gpc123456/SmartClock/GUI_Picture/ConfigWiFiSuccess.bmp

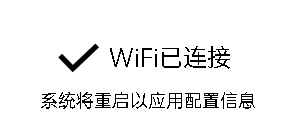
GUI_Picture/ConfigWiFiSuccess.bmp
