gpc123456/SmartClock/GUI_Picture/Pomodoro_HomePage.bmp

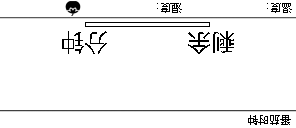
GUI_Picture/Pomodoro_HomePage.bmp
