gpc123456/SmartClock/GUI_Picture/Pomodoro_StartPage.bmp

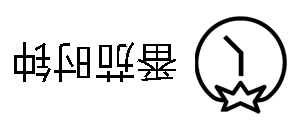
GUI_Picture/Pomodoro_StartPage.bmp
