gpc123456/SmartClock/GUI_Picture/StartPage.bmp

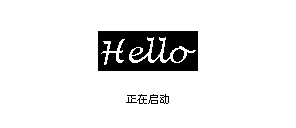
GUI_Picture/StartPage.bmp
