gpc123456/SmartClock/src/TimeNumber.h

#ifndef TIMENUMBER_H
#define TIMENUMBER_H

#include <Arduino.h>

const PROGMEM uint8_t Num_0[]={
 /* 0X81,0X01,0X28,0X00,0X40,0X00, */
0XFF,0XFF,0XFF,0XFF,0XFF,0XFF,0XFF,0XFF,0XFF,0XFF,0XFF,0X80,0X01,0XFF,0XFF,0XFF,
0XFF,0XFF,0XE0,0X00,0X00,0X07,0XFF,0XFF,0XFF,0XFE,0X00,0X00,0X00,0X00,0XFF,0XFF,
0XFF,0XF8,0X00,0X00,0X00,0X00,0X1F,0XFF,0XFF,0XE0,0X00,0X00,0X00,0X00,0X07,0XFF,
0XFF,0X80,0X00,0X1F,0XF0,0X00,0X01,0XFF,0XFF,0X00,0X0F,0XFF,0XFF,0XF0,0X00,0XFF,
0XFE,0X00,0XFF,0XFF,0XFF,0XFF,0X00,0X7F,0XFC,0X03,0XFF,0XFF,0XFF,0XFF,0XC0,0X3F,
0XF8,0X0F,0XFF,0XFF,0XFF,0XFF,0XF0,0X1F,0XF0,0X1F,0XFF,0XFF,0XFF,0XFF,0XF8,0X1F,
0XF0,0X3F,0XFF,0XFF,0XFF,0XFF,0XFC,0X0F,0XE0,0X7F,0XFF,0XFF,0XFF,0XFF,0XFE,0X0F,
0XE0,0XFF,0XFF,0XFF,0XFF,0XFF,0XFF,0X07,0XE0,0XFF,0XFF,0XFF,0XFF,0XFF,0XFF,0X07,
0XC1,0XFF,0XFF,0XFF,0XFF,0XFF,0XFF,0X87,0XC1,0XFF,0XFF,0XFF,0XFF,0XFF,0XFF,0X83,
0XC1,0XFF,0XFF,0XFF,0XFF,0XFF,0XFF,0X83,0XC1,0XFF,0XFF,0XFF,0XFF,0XFF,0XFF,0X83,
0XC1,0XFF,0XFF,0XFF,0XFF,0XFF,0XFF,0X83,0XC1,0XFF,0XFF,0XFF,0XFF,0XFF,0XFF,0X83,
0XC1,0XFF,0XFF,0XFF,0XFF,0XFF,0XFF,0X83,0XC1,0XFF,0XFF,0XFF,0XFF,0XFF,0XFF,0X83,
0XC1,0XFF,0XFF,0XFF,0XFF,0XFF,0XFF,0X87,0XE0,0XFF,0XFF,0XFF,0XFF,0XFF,0XFF,0X07,
0XE0,0XFF,0XFF,0XFF,0XFF,0XFF,0XFF,0X07,0XE0,0X7F,0XFF,0XFF,0XFF,0XFF,0XFE,0X0F,
0XF0,0X3F,0XFF,0XFF,0XFF,0XFF,0XFC,0X0F,0XF0,0X1F,0XFF,0XFF,0XFF,0XFF,0XF8,0X1F,
0XF8,0X0F,0XFF,0XFF,0XFF,0XFF,0XF0,0X1F,0XFC,0X03,0XFF,0XFF,0XFF,0XFF,0XC0,0X3F,
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
0X01,0XFF,0XF8,0X1F,0XFF,0XFF,0XF0,0X00,0X7F,0XF0,0X1F,0XFF,0XFF,0XFC,0X00,0X00,
0X00,0X3F,0XFF,0XFF,0XFF,0X00,0X00,0X00,0X7F,0XFF,0XFF,0XFF,0XC0,0X00,0X01,0XFF,
0XFF,0XFF,0XFF,0XF8,0X00,0X07,0XFF,0XFF,0XFF,0XFF,0XFF,0X00,0X3F,0XFF,0XFF,0XFF,
0XFF,0XFF,0XFF,0XFF,0XFF,};

#endif
