gpc123456/SmartClock/src/WeatherIcon.h

#ifndef WEATHERICON_H
#define WEATHERICON_H

#include <Arduino.h>

const PROGMEM uint8_t WCode_0[]={
/* 0X81,0X01,0X32,0X00,0X30,0X00, */
0XFF,0XFF,0XFF,0XFF,0XFF,0XFF,0XFF,0XFF,0XFF,0XFF,0XFF,0XFF,0XFF,0XFF,0XFF,0XFF,
0XFF,0XFF,0XFF,0XFF,0XFF,0XFF,0XFF,0XFF,0XFF,0XFF,0XFF,0XFF,0XFF,0XFF,0XFF,0XFF,
0XFF,0XFF,0XFF,0XFF,0XFF,0XFF,0XFF,0XFF,0XFF,0XFF,0XFF,0XF0,0X01,0XFF,0XFF,0XFF,
0XFF,0XC0,0X00,0X7F,0XFF,0XFF,0XFF,0X00,0X00,0X1F,0XFF,0XFF,0XFE,0X00,0X00,0X0F,
0XFF,0XFF,0XF8,0X00,0X00,0X03,0XFF,0XFF,0XF0,0X00,0X00,0X01,0XFF,0XFF,0XF0,0X00,
0X00,0X01,0XFF,0XFF,0XE0,0X00,0X00,0X00,0XFF,0XFF,0XC0,0X00,0X00,0X00,0X7F,0XFF,
0XC0,0X00,0X00,0X00,0X7F,0XFF,0X80,0X00,0X00,0X00,0X3F,0XFF,0X80,0X00,0X00,0X00,
0X3F,0XFF,0X00,0X00,0X00,0X00,0X1F,0XFF,0X00,0X00,0X00,0X00,0X1F,0XFF,0X00,0X00,
0X00,0X00,0X19,0X53,0X00,0X00,0X00,0X00,0X19,0X25,0X00,0X00,0X00,0X00,0X19,0X25,
0X00,0X00,0X00,0X00,0X10,0X27,0X00,0X00,0X00,0X00,0X19,0X27,0X00,0X00,0X00,0X00,
0X19,0X41,0X00,0X00,0X00,0X00,0X1F,0X7F,0X00,0X00,0X00,0X00,0X18,0X03,0X00,0X00,
0X00,0X00,0X1B,0XBB,0X80,0X00,0X00,0X00,0X38,0X03,0X80,0X00,0X00,0X00,0X3F,0XFF,
0XC0,0X00,0X00,0X00,0X7F,0XFF,0XC0,0X00,0X00,0X00,0X7F,0XFF,0XE0,0X00,0X00,0X00,
0XFF,0XFF,0XF0,0X00,0X00,0X01,0XFF,0XFF,0XF0,0X00,0X00,0X01,0XFF,0XFF,0XF8,0X00,
0X00,0X03,0XFF,0XFF,0XFE,0X00,0X00,0X0F,0XFF,0XFF,0XFF,0X00,0X00,0X1F,0XFF,0XFF,
0XFF,0XC0,0X00,0X7F,0XFF,0XFF,0XFF,0XF0,0X01,0XFF,0XFF,0XFF,0XFF,0XFF,0XFF,0XFF,
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
0XDE,0XFB,0XDE,0XFB,0XDE,0XFB,0XDE,0XFB,0XC0,0X03,0XFF,0XFF,0XFF,0XFF,0XFF,0XFF,
0XFF,0XFF,0XFF,0XFF,0X80,0X03,0XBB,0XBB,0XBB,0XBB,0XBB,0XBF,0X80,0X3F,0XFF,0XC7,
0XFF,0XF3,0XC0,0X0D,0XDD,0XEF,0XDD,0XEF,0XC0,0X0F,0XFF,0XFF,0XFF,0XFF,0XFF,0XFF,};

#endif
