gpc123456/SmartClock/src/strings_en.h

/**
 * strings_en.h
 * engligh strings for
 * WiFiManager, a library for the ESP8266/Arduino platform
 * for configuration of WiFi credentials using a Captive Portal
 * 
 * @author Creator tzapu
 * @author tablatronix
 * @version 0.0.0
 * @license MIT
 */

#ifndef _WM_STRINGS_H_
#define _WM_STRINGS_H_

#ifndef WIFI_MANAGER_OVERRIDE_STRINGS
// !!! ABOVE WILL NOT WORK if you define in your sketch, must be build flag, if anyone one knows how to order includes to be able to do this it would be neat.. I have seen it done..

const char HTTP_HEAD_START[]       PROGMEM = "<!DOCTYPE html>"
"<html lang='zh-CN'><head>"
"<meta name='format-detection' content='telephone=no'>"
"<meta charset='UTF-8'>"
"<meta  name='viewport' content='width=device-width,initial-scale=1,user-scalable=no'/>"
"<title>{v}</title>";

const char HTTP_SCRIPT[]           PROGMEM = "<script>function c(l){"
"document.getElementById('s').value=l.innerText||l.textContent;"
"p = l.nextElementSibling.classList.contains('l');"
"document.getElementById('p').disabled = !p;"
"if(p)document.getElementById('p').focus();}</script>"; // @todo add button states, disable on click , show ack , spinner etc

const char HTTP_HEAD_END[]         PROGMEM = "</head><body class='{c}'><div class='wrap'>"; // {c} = _bodyclass
// example of embedded logo, base64 encoded inline, No styling here
// const char HTTP_ROOT_MAIN[]        PROGMEM = "<img title=' alt=' src='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' /><h1>{v}</h1><h3>WiFiManager</h3>";
const char HTTP_ROOT_MAIN[]        PROGMEM = "<h1>{t}</h1><h3>{v}</h3>";
const char * const HTTP_PORTAL_MENU[] PROGMEM = {
"<form action='/wifi'    method='get'><button>&#x4E00;&#x952E;&#x8FDE;&#x63A5;WIFI</button></form><br/>\n", // MENU_WIFI
"<form action='/0wifi'   method='get'></form><br/>\n", // MENU_WIFINOSCAN
"<form action='/info'    method='get'></form><br/>\n", // MENU_INFO
"<form action='/param'   method='get'></form><br/>\n",//MENU_PARAM
"<form action='/close'   method='get'></form><br/>\n", // MENU_CLOSE
"<form action='/restart' method='get'></form><br/>\n",// MENU_RESTART
"<form action='/exit'    method='get'></form><br/>\n",  // MENU_EXIT
"<form action='/erase'   method='get'></form><br/>\n", // MENU_ERASE
"<form action='/update'  method='get'></form><br/>\n",// MENU_UPDATE
"<hr><br/>" // MENU_SEP
};

// const char HTTP_PORTAL_OPTIONS[]   PROGMEM = strcat(HTTP_PORTAL_MENU[0] , HTTP_PORTAL_MENU[3] , HTTP_PORTAL_MENU[7]);
const char HTTP_PORTAL_OPTIONS[]   PROGMEM = "";
const char HTTP_ITEM_QI[]          PROGMEM = "<div role='img' aria-label='{r}%' title='{r}%' class='q q-{q} {i} {h}'></div>"; // rssi icons
const char HTTP_ITEM_QP[]          PROGMEM = "<div class='q {h}'>{r}%</div>"; // rssi percentage {h} = hidden showperc pref
const char HTTP_ITEM[]             PROGMEM = "<div><a href='#p' onclick='c(this)'>{v}</a>{qi}{qp}</div>"; // {q} = HTTP_ITEM_QI, {r} = HTTP_ITEM_QP
// const char HTTP_ITEM[]            PROGMEM = "<div><a href='#p' onclick='c(this)'>{v}</a> {R} {r}% {q} {e}</div>"; // test all tokens

const char HTTP_FORM_START[]       PROGMEM = "<form method='POST' action='{v}'>";


const char HTTP_FORM_WIFI[]        PROGMEM = "<label for='s'>WIFI&#x540D;&#x79F0;&#xFF0C;&#x53EF;&#x70B9;&#x51FB;&#x5217;&#x8868;&#x4E2D;WIFI&#x8FDB;&#x884C;&#x9009;&#x62E9;</label><input id='s' name='s' maxlength='32' autocorrect='off' autocapitalize='none'><br/><label for='p'>WIFI&#x5BC6;&#x7801;</label><input id='p' name='p' maxlength='64' type='password'>";
const char HTTP_FORM_WIFI_END[]    PROGMEM = "";
const char HTTP_FORM_STATIC_HEAD[] PROGMEM = "<hr><br/>";

const char HTTP_FORM_END[]         PROGMEM = "<br/><br/><button type='submit'>&#x786E;&#x5B9A;</button></form>";
const char HTTP_FORM_LABEL[]       PROGMEM = "<label for='{i}'>{t}</label>";
const char HTTP_FORM_PARAM_HEAD[]  PROGMEM = "<hr><br/>";
const char HTTP_FORM_PARAM[]       PROGMEM = "<br/><input id='{i}' name='{n}' maxlength='{l}' value='{v}' {c}>";

const char HTTP_SCAN_LINK[]        PROGMEM = "<br/><form action='/wifi?refresh=1' method='POST'><button name='refresh' value='1'>&#x5237;&#x65B0;</button></form>";

const char HTTP_SAVED[]            PROGMEM = "<div class='msg'>&#x5DF2;&#x4FDD;&#x5B58;&#x60A8;&#x7684;WIFI&#x4FE1;&#x606F;<br/>&#x6B63;&#x5728;&#x5C1D;&#x8BD5;&#x8FDE;&#x63A5;WIFI.<br />&#x8BF7;&#x7559;&#x610F;&#x663E;&#x793A;&#x5C4F;&#x4E0A;&#x7684;&#x63D0;&#x793A;&#xFF0C;&#x5982;&#x679C;&#x8FDE;&#x63A5;&#x5931;&#x8D25;&#xFF0C;&#x8BF7;&#x518D;&#x6B21;&#x8FDE;&#x63A5;&#x672C;WIFI&#x91CD;&#x65B0;&#x914D;&#x7F6E;&#x7F51;&#x7EDC;.</div>";

const char HTTP_PARAMSAVED[]       PROGMEM = "<div class='msg S'>WIFI&#x7F51;&#x7EDC;&#x4FE1;&#x606F;&#x5DF2;&#x66F4;&#x65B0;.<br/></div>";
const char HTTP_END[]              PROGMEM = "</div></body></html>";
const char HTTP_ERASEBTN[]         PROGMEM = "<br/><form action='/erase' method='get'><button class='D'>Erase WiFi Config</button></form>";
const char HTTP_UPDATEBTN[]        PROGMEM = "<br/><form action='/update' method='get'><button>Update</button></form>";
const char HTTP_BACKBTN[]          PROGMEM = "<hr><br/><form action='/' method='get'><button>Back</button></form>";

const char HTTP_STATUS_ON[]        PROGMEM = "<div class='msg S'><strong>&#x5DF2;&#x8FDE;&#x63A5;</strong> &#x5230; {v}<br/><em><small>with IP {i}</small></em></div>";
const char HTTP_STATUS_OFF[]       PROGMEM = "<div class='msg {c}'><strong>&#x672A;&#x8FDE;&#x63A5;</strong> &#x5230; {v}{r}</div>"; // {c=class} {v=ssid} {r=status_off}
const char HTTP_STATUS_OFFPW[]     PROGMEM = "<br/>Authentication Failure"; // STATION_WRONG_PASSWORD,  no eps32
const char HTTP_STATUS_OFFNOAP[]   PROGMEM = "<br/>&#x65E0;&#x53EF;&#x8FDE;&#x63A5;&#x7684;WIFI";   // WL_NO_SSID_AVAIL
const char HTTP_STATUS_OFFFAIL[]   PROGMEM = "<br/>&#x65E0;&#x6CD5;&#x8FDE;&#x63A5;"; // WL_CONNECT_FAILED
const char HTTP_STATUS_NONE[]      PROGMEM = "<div class='msg'>&#x8FD8;&#x672A;&#x8BBE;&#x7F6E;WIFI&#x7F51;&#x7EDC;&#x4FE1;&#x606F;</div>";
const char HTTP_BR[]               PROGMEM = "<br/>";

const char HTTP_STYLE[]            PROGMEM = "<style>"
".c,body{text-align:center;font-family:verdana}div,input{padding:5px;font-size:1em;margin:5px 0;box-sizing:border-box;}"
"input,button,.msg{border-radius:.3rem;width: 100%},input[type=radio]{width: auto}"
"button,input[type='button'],input[type='submit']{cursor:pointer;border:0;background-color:#1fa3ec;color:#fff;line-height:2.4rem;font-size:1.2rem;width:100%}"
"input[type='file']{border:1px solid #1fa3ec}"
".wrap {text-align:left;display:inline-block;min-width:260px;max-width:500px}"
// links
"a{color:#000;font-weight:700;text-decoration:none}a:hover{color:#1fa3ec;text-decoration:underline}"
// quality icons
".q{height:16px;margin:0;padding:0 5px;text-align:right;min-width:38px;float:right}.q.q-0:after{background-position-x:0}.q.q-1:after{background-position-x:-16px}.q.q-2:after{background-position-x:-32px}.q.q-3:after{background-position-x:-48px}.q.q-4:after{background-position-x:-64px}.q.l:before{background-position-x:-80px;padding-right:5px}.ql .q{float:left}.q:after,.q:before{content:'';width:16px;height:16px;display:inline-block;background-repeat:no-repeat;background-position: 16px 0;"
"background-image:url('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');}"
// icons @2x media query (32px rescaled)
"@media (-webkit-min-device-pixel-ratio: 2),(min-resolution: 192dpi){.q:before,.q:after {"
"background-image:url('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');"
"background-size: 95px 16px;}}"
// msg callouts
".msg{padding:20px;margin:20px 0;border:1px solid #eee;border-left-width:5px;border-left-color:#777}.msg h4{margin-top:0;margin-bottom:5px}.msg.P{border-left-color:#1fa3ec}.msg.P h4{color:#1fa3ec}.msg.D{border-left-color:#dc3630}.msg.D h4{color:#dc3630}.msg.S{border-left-color: #5cb85c}.msg.S h4{color: #5cb85c}"
// lists
"dt{font-weight:bold}dd{margin:0;padding:0 0 0.5em 0;min-height:12px}"
"td{vertical-align: top;}"
".h{display:none}"
"button.D{background-color:#dc3630}"
// invert
"body.invert,body.invert a,body.invert h1 {background-color:#060606;color:#fff;}"
"body.invert .msg{color:#fff;background-color:#282828;border-top:1px solid #555;border-right:1px solid #555;border-bottom:1px solid #555;}"
"body.invert .q[role=img]{-webkit-filter:invert(1);filter:invert(1);}"
"input:disabled {opacity: 0.5;}"
"</style>";

#ifndef WM_NOHELP
const char HTTP_HELP[]             PROGMEM =
 "<br/><h3>Available Pages</h3><hr>"
 "<table class='table'>"
 "<thead><tr><th>Page</th><th>Function</th></tr></thead><tbody>"
 "<tr><td><a href='/'>/</a></td>"
 "<td>Menu page.</td></tr>"
 "<tr><td><a href='/wifi'>/wifi</a></td>"
 "<td>Show WiFi scan results and enter WiFi configuration.(/0wifi noscan)</td></tr>"
 "<tr><td><a href='/wifisave'>/wifisave</a></td>"
 "<td>Save WiFi configuration information and configure device. Needs variables supplied.</td></tr>"
 "<tr><td><a href='/param'>/param</a></td>"
 "<td>Parameter page</td></tr>"
 "<tr><td><a href='/info'>/info</a></td>"
 "<td>Information page</td></tr>"
 "<tr><td><a href='/u'>/u</a></td>"
 "<td>OTA Update</td></tr>"
 "<tr><td><a href='/close'>/close</a></td>"
 "<td>Close the captiveportal popup,configportal will remain active</td></tr>"
 "<tr><td>/exit</td>"
 "<td>Exit Config Portal, configportal will close</td></tr>"
 "<tr><td>/restart</td>"
 "<td>Reboot the device</td></tr>"
 "<tr><td>/erase</td>"
 "<td>Erase WiFi configuration and reboot Device. Device will not reconnect to a network until new WiFi configuration data is entered.</td></tr>"
 "</table>"
 "<p/>More information about WiFiManager at <a href='https://github.com/tzapu/WiFiManager'>https://github.com/tzapu/WiFiManager</a>.";
#else
const char HTTP_HELP[]             PROGMEM = "";
#endif

const char HTTP_UPDATE[] PROGMEM = "Upload New Firmware<br/><form method='POST' action='u' enctype='multipart/form-data' onchange=\"(function(el){document.getElementById('uploadbin').style.display = el.value=='' ? 'none' : 'initial';})(this)\"><input type='file' name='update' accept='.bin,application/octet-stream'><button id='uploadbin' type='submit' class='h D'>Update</button></form><small><a href='http://192.168.4.1/update' target='_blank'>* May not function inside captive portal, Open in browser http://192.168.4.1</a><small>";
const char HTTP_UPDATE_FAIL[] PROGMEM = "<div class='msg D'><strong>Update Failed!</strong><Br/>Reboot device and try again</div>";
const char HTTP_UPDATE_SUCCESS[] PROGMEM = "<div class='msg S'><strong>Update Successful.  </strong> <br/> Device Rebooting now...</div>";

#ifdef WM_JSTEST
const char HTTP_JS[] PROGMEM = 
"<script>function postAjax(url, data, success) {"
"    var params = typeof data == 'string' ? data : Object.keys(data).map("
"            function(k){ return encodeURIComponent(k) + '=' + encodeURIComponent(data[k]) }"
"        ).join('&');"
"    var xhr = window.XMLHttpRequest ? new XMLHttpRequest() : new ActiveXObject(\"Microsoft.XMLHTTP\");"
"    xhr.open('POST', url);"
"    xhr.onreadystatechange = function() {"
"        if (xhr.readyState>3 && xhr.status==200) { success(xhr.responseText); }"
"    };"
"    xhr.setRequestHeader('X-Requested-With', 'XMLHttpRequest');"
"    xhr.setRequestHeader('Content-Type', 'application/x-www-form-urlencoded');"
"    xhr.send(params);"
"    return xhr;}"
"postAjax('/status', 'p1=1&p2=Hello+World', function(data){ console.log(data); });"
"postAjax('/status', { p1: 1, p2: 'Hello World' }, function(data){ console.log(data); });"
"</script>";
#endif

// Info html
#ifdef ESP32
	const char HTTP_INFO_esphead[]    PROGMEM = "<h3>esp32</h3><hr><dl>";
	const char HTTP_INFO_chiprev[]    PROGMEM = "<dt>Chip Rev</dt><dd>{1}</dd>";
  	const char HTTP_INFO_lastreset[]  PROGMEM = "<dt>Last reset reason</dt><dd>CPU0: {1}<br/>CPU1: {2}</dd>";
  	const char HTTP_INFO_aphost[]     PROGMEM = "<dt>Acccess Point Hostname</dt><dd>{1}</dd>";  
    const char HTTP_INFO_psrsize[]    PROGMEM = "<dt>PSRAM Size</dt><dd>{1} bytes</dd>";
	const char HTTP_INFO_temp[]       PROGMEM = "<dt>Temperature</dt><dd>{1} C&deg; / {2} F&deg;</dd><dt>Hall</dt><dd>{3}</dd>";    
#else
	const char HTTP_INFO_esphead[]    PROGMEM = "<h3>esp8266</h3><hr><dl>";
	const char HTTP_INFO_fchipid[]    PROGMEM = "<dt>Flash Chip ID</dt><dd>{1}</dd>";
	const char HTTP_INFO_corever[]    PROGMEM = "<dt>Core Version</dt><dd>{1}</dd>";
	const char HTTP_INFO_bootver[]    PROGMEM = "<dt>Boot Version</dt><dd>{1}</dd>";
	const char HTTP_INFO_lastreset[]  PROGMEM = "<dt>Last reset reason</dt><dd>{1}</dd>";
	const char HTTP_INFO_flashsize[]  PROGMEM = "<dt>Real Flash Size</dt><dd>{1} bytes</dd>";
#endif

const char HTTP_INFO_memsmeter[]  PROGMEM = "<br/><progress value='{1}' max='{2}'></progress></dd>";
const char HTTP_INFO_memsketch[]  PROGMEM = "<dt>Memory - Sketch Size</dt><dd>Used / Total bytes<br/>{1} / {2}";
const char HTTP_INFO_freeheap[]   PROGMEM = "<dt>Memory - Free Heap</dt><dd>{1} bytes available</dd>"; 
const char HTTP_INFO_wifihead[]   PROGMEM = "<br/><h3>WiFi</h3><hr>";
const char HTTP_INFO_uptime[]     PROGMEM = "<dt>Uptime</dt><dd>{1} Mins {2} Secs</dd>";
const char HTTP_INFO_chipid[]     PROGMEM = "<dt>Chip ID</dt><dd>{1}</dd>";
const char HTTP_INFO_idesize[]    PROGMEM = "<dt>Flash Size</dt><dd>{1} bytes</dd>";
const char HTTP_INFO_sdkver[]     PROGMEM = "<dt>SDK Version</dt><dd>{1}</dd>";
const char HTTP_INFO_cpufreq[]    PROGMEM = "<dt>CPU Frequency</dt><dd>{1}MHz</dd>";
const char HTTP_INFO_apip[]       PROGMEM = "<dt>Access Point IP</dt><dd>{1}</dd>";
const char HTTP_INFO_apmac[]      PROGMEM = "<dt>Access Point MAC</dt><dd>{1}</dd>";
const char HTTP_INFO_apssid[]     PROGMEM = "<dt>Access Point SSID</dt><dd>{1}</dd>";
const char HTTP_INFO_apbssid[]    PROGMEM = "<dt>BSSID</dt><dd>{1}</dd>";
const char HTTP_INFO_stassid[]    PROGMEM = "<dt>Station SSID</dt><dd>{1}</dd>";
const char HTTP_INFO_staip[]      PROGMEM = "<dt>Station IP</dt><dd>{1}</dd>";
const char HTTP_INFO_stagw[]      PROGMEM = "<dt>Station Gateway</dt><dd>{1}</dd>";
const char HTTP_INFO_stasub[]     PROGMEM = "<dt>Station Subnet</dt><dd>{1}</dd>";
const char HTTP_INFO_dnss[]       PROGMEM = "<dt>DNS Server</dt><dd>{1}</dd>";
const char HTTP_INFO_host[]       PROGMEM = "<dt>Hostname</dt><dd>{1}</dd>";
const char HTTP_INFO_stamac[]     PROGMEM = "<dt>Station MAC</dt><dd>{1}</dd>";
const char HTTP_INFO_conx[]       PROGMEM = "<dt>Connected</dt><dd>{1}</dd>";
const char HTTP_INFO_autoconx[]   PROGMEM = "<dt>Autoconnect</dt><dd>{1}</dd>";


const char S_brand[]              PROGMEM = "&#x6B22;&#x8FCE;&#x4F7F;&#x7528;";

const char S_debugPrefix[]        PROGMEM = "*wm:";
const char S_y[]                  PROGMEM = "Yes";
const char S_n[]                  PROGMEM = "No";
const char S_enable[]             PROGMEM = "Enabled";
const char S_disable[]            PROGMEM = "Disabled";
const char S_GET[]                PROGMEM = "GET";
const char S_POST[]               PROGMEM = "POST";
const char S_NA[]                 PROGMEM = "Unknown";
const char S_passph[]             PROGMEM = "********";
const char S_titlewifisaved[]     PROGMEM = "Credentials Saved";
const char S_titlewifisettings[]  PROGMEM = "Settings Saved";
const char S_titlewifi[]          PROGMEM = "Config ESP";
const char S_titleinfo[]          PROGMEM = "Info";
const char S_titleparam[]         PROGMEM = "Setup";
const char S_titleparamsaved[]    PROGMEM = "Setup Saved";
const char S_titleexit[]          PROGMEM = "Exit";
const char S_titlereset[]         PROGMEM = "Reset";
const char S_titleerase[]         PROGMEM = "Erase";
const char S_titleclose[]         PROGMEM = "Close";
const char S_options[]            PROGMEM = "options";

const char S_nonetworks[]         PROGMEM = "&#x6CA1;&#x6709;&#x641C;&#x7D22;&#x5230;WIFI&#x7F51;&#x7EDC;&#xFF0C;&#x8BF7;&#x70B9;&#x51FB;&#x5237;&#x65B0;&#x91CD;&#x8BD5;.";
const char S_staticip[]           PROGMEM = "Static IP";
const char S_staticgw[]           PROGMEM = "Static Gateway";
const char S_staticdns[]          PROGMEM = "Static DNS";
const char S_subnet[]             PROGMEM = "Subnet";
const char S_exiting[]            PROGMEM = "Exiting";
const char S_resetting[]          PROGMEM = "Module will reset in a few seconds.";
const char S_closing[]            PROGMEM = "You can close the page, portal will continue to run";
const char S_error[]              PROGMEM = "An Error Occured";
const char S_notfound[]           PROGMEM = "File Not Found\n\n";
const char S_uri[]                PROGMEM = "URI: ";
const char S_method[]             PROGMEM = "\nMethod: ";
const char S_args[]               PROGMEM = "\nArguments: ";
const char S_parampre[]           PROGMEM = "param_";

// debug strings
const char D_HR[]                 PROGMEM = "--------------------";

// END WIFI_MANAGER_OVERRIDE_STRINGS
#endif

// -----------------------------------------------------------------------------------------------
// DO NOT EDIT BELOW THIS LINE

const uint8_t _nummenutokens = 10;
const char * const _menutokens[10] PROGMEM = {
    "wifi",
    "wifinoscan",
    "info",
    "param",
    "close",
    "restart",
    "exit",
    "erase",
    "update",
    "sep"
};

const char R_root[]               PROGMEM = "/";
const char R_wifi[]               PROGMEM = "/wifi";
const char R_wifinoscan[]         PROGMEM = "/0wifi";
const char R_wifisave[]           PROGMEM = "/wifisave";
const char R_info[]               PROGMEM = "/info";
const char R_param[]              PROGMEM = "/param";
const char R_paramsave[]          PROGMEM = "/paramsave";
const char R_restart[]            PROGMEM = "/restart";
const char R_exit[]               PROGMEM = "/exit";
const char R_close[]              PROGMEM = "/close";
const char R_erase[]              PROGMEM = "/erase"; 
const char R_status[]             PROGMEM = "/status";
const char R_update[]             PROGMEM = "/update";
const char R_updatedone[]         PROGMEM = "/u";


//Strings
const char S_ip[]                 PROGMEM = "ip";
const char S_gw[]                 PROGMEM = "gw";
const char S_sn[]                 PROGMEM = "sn";
const char S_dns[]                PROGMEM = "dns";

// softap ssid default prefix
#ifdef ESP8266
	const char S_ssidpre[]        PROGMEM = "ESP";
#elif defined(ESP32)
	const char S_ssidpre[]        PROGMEM = "ESP32";
#else
	const char S_ssidpre[]        PROGMEM = "WM";
#endif

//Tokens
//@todo consolidate and reduce
const char T_ss[]                 PROGMEM = "{"; // token start sentinel
const char T_es[]                 PROGMEM = "}"; // token end sentinel
const char T_1[]                  PROGMEM = "{1}"; // @token 1
const char T_2[]                  PROGMEM = "{2}"; // @token 2
const char T_3[]                  PROGMEM = "{3}"; // @token 2
const char T_v[]                  PROGMEM = "{v}"; // @token v
const char T_I[]                  PROGMEM = "{I}"; // @token I
const char T_i[]                  PROGMEM = "{i}"; // @token i
const char T_n[]                  PROGMEM = "{n}"; // @token n
const char T_p[]                  PROGMEM = "{p}"; // @token p
const char T_t[]                  PROGMEM = "{t}"; // @token t
const char T_l[]                  PROGMEM = "{l}"; // @token l
const char T_c[]                  PROGMEM = "{c}"; // @token c
const char T_e[]                  PROGMEM = "{e}"; // @token e
const char T_q[]                  PROGMEM = "{q}"; // @token q
const char T_r[]                  PROGMEM = "{r}"; // @token r
const char T_R[]                  PROGMEM = "{R}"; // @token R
const char T_h[]                  PROGMEM = "{h}"; // @token h

// http
const char HTTP_HEAD_CL[]         PROGMEM = "Content-Length";
const char HTTP_HEAD_CT[]         PROGMEM = "text/html";
const char HTTP_HEAD_CT2[]        PROGMEM = "text/plain";
const char HTTP_HEAD_CORS[]       PROGMEM = "Access-Control-Allow-Origin";
const char HTTP_HEAD_CORS_ALLOW_ALL[]  PROGMEM = "*";

const char * const WIFI_STA_STATUS[] PROGMEM
{
  "WL_IDLE_STATUS",     // 0 STATION_IDLE
  "WL_NO_SSID_AVAIL",   // 1 STATION_NO_AP_FOUND
  "WL_SCAN_COMPLETED",  // 2
  "WL_CONNECTED",       // 3 STATION_GOT_IP
  "WL_CONNECT_FAILED",  // 4 STATION_CONNECT_FAIL, STATION_WRONG_PASSWORD(NI)
  "WL_CONNECTION_LOST", // 5
  "WL_DISCONNECTED",    // 6 
  "WL_STATION_WRONG_PASSWORD" // 7 KLUDGE 
};

#ifdef ESP32
const char * const AUTH_MODE_NAMES[] PROGMEM
{
    "OPEN",
    "WEP",             
    "WPA_PSK",         
    "WPA2_PSK",        
    "WPA_WPA2_PSK",    
    "WPA2_ENTERPRISE", 
    "MAX"
};
#elif defined(ESP8266)
const char * const AUTH_MODE_NAMES[] PROGMEM
{
    "",
    "",
    "WPA_PSK",      // 2 ENC_TYPE_TKIP
    "",
    "WPA2_PSK",     // 4 ENC_TYPE_CCMP
    "WEP",          // 5 ENC_TYPE_WEP
    "",
    "OPEN",         //7 ENC_TYPE_NONE
    "WPA_WPA2_PSK", // 8 ENC_TYPE_AUTO
};
#endif

const char* const WIFI_MODES[] PROGMEM = { "NULL", "STA", "AP", "STA+AP" };


#ifdef ESP32
// as 2.5.2
// typedef struct {
//     char                  cc[3];   /**< country code string */
//     uint8_t               schan;   /**< start channel */
//     uint8_t               nchan;   /**< total channel number */
//     int8_t                max_tx_power;   /**< This field is used for getting WiFi maximum transmitting power, call esp_wifi_set_max_tx_power to set the maximum transmitting power. */
//     wifi_country_policy_t policy;  /**< country policy */
// } wifi_country_t;
const wifi_country_t WM_COUNTRY_US{"US",1,11,CONFIG_ESP32_PHY_MAX_WIFI_TX_POWER,WIFI_COUNTRY_POLICY_AUTO};
const wifi_country_t WM_COUNTRY_CN{"CN",1,13,CONFIG_ESP32_PHY_MAX_WIFI_TX_POWER,WIFI_COUNTRY_POLICY_AUTO};
const wifi_country_t WM_COUNTRY_JP{"JP",1,14,CONFIG_ESP32_PHY_MAX_WIFI_TX_POWER,WIFI_COUNTRY_POLICY_AUTO};
#elif defined(ESP8266) && !defined(WM_NOCOUNTRY)
// typedef struct {
//     char cc[3];               /**< country code string */
//     uint8_t schan;            /**< start channel */
//     uint8_t nchan;            /**< total channel number */
//     uint8_t policy;           /**< country policy */
// } wifi_country_t;
const wifi_country_t WM_COUNTRY_US{"US",1,11,WIFI_COUNTRY_POLICY_AUTO};
const wifi_country_t WM_COUNTRY_CN{"CN",1,13,WIFI_COUNTRY_POLICY_AUTO};
const wifi_country_t WM_COUNTRY_JP{"JP",1,14,WIFI_COUNTRY_POLICY_AUTO};
#endif


/*
* ESP32 WiFi Events

0  SYSTEM_EVENT_WIFI_READY               < ESP32 WiFi ready
1  SYSTEM_EVENT_SCAN_DONE                < ESP32 finish scanning AP
2  SYSTEM_EVENT_STA_START                < ESP32 station start
3  SYSTEM_EVENT_STA_STOP                 < ESP32 station stop
4  SYSTEM_EVENT_STA_CONNECTED            < ESP32 station connected to AP
5  SYSTEM_EVENT_STA_DISCONNECTED         < ESP32 station disconnected from AP
6  SYSTEM_EVENT_STA_AUTHMODE_CHANGE      < the auth mode of AP connected by ESP32 station changed
7  SYSTEM_EVENT_STA_GOT_IP               < ESP32 station got IP from connected AP
8  SYSTEM_EVENT_STA_LOST_IP              < ESP32 station lost IP and the IP is reset to 0
9  SYSTEM_EVENT_STA_WPS_ER_SUCCESS       < ESP32 station wps succeeds in enrollee mode
10 SYSTEM_EVENT_STA_WPS_ER_FAILED        < ESP32 station wps fails in enrollee mode
11 SYSTEM_EVENT_STA_WPS_ER_TIMEOUT       < ESP32 station wps timeout in enrollee mode
12 SYSTEM_EVENT_STA_WPS_ER_PIN           < ESP32 station wps pin code in enrollee mode
13 SYSTEM_EVENT_AP_START                 < ESP32 soft-AP start
14 SYSTEM_EVENT_AP_STOP                  < ESP32 soft-AP stop
15 SYSTEM_EVENT_AP_STACONNECTED          < a station connected to ESP32 soft-AP
16 SYSTEM_EVENT_AP_STADISCONNECTED       < a station disconnected from ESP32 soft-AP
17 SYSTEM_EVENT_AP_STAIPASSIGNED         < ESP32 soft-AP assign an IP to a connected station
18 SYSTEM_EVENT_AP_PROBEREQRECVED        < Receive probe request packet in soft-AP interface
19 SYSTEM_EVENT_GOT_IP6                  < ESP32 station or ap or ethernet interface v6IP addr is preferred
20 SYSTEM_EVENT_ETH_START                < ESP32 ethernet start
21 SYSTEM_EVENT_ETH_STOP                 < ESP32 ethernet stop
22 SYSTEM_EVENT_ETH_CONNECTED            < ESP32 ethernet phy link up
23 SYSTEM_EVENT_ETH_DISCONNECTED         < ESP32 ethernet phy link down
24 SYSTEM_EVENT_ETH_GOT_IP               < ESP32 ethernet got IP from connected AP
25 SYSTEM_EVENT_MAX


typedef enum {
    ARDUINO_EVENT_WIFI_READY = 0,
    ARDUINO_EVENT_WIFI_SCAN_DONE,
    ARDUINO_EVENT_WIFI_STA_START,
    ARDUINO_EVENT_WIFI_STA_STOP,
    ARDUINO_EVENT_WIFI_STA_CONNECTED,
    ARDUINO_EVENT_WIFI_STA_DISCONNECTED,
    ARDUINO_EVENT_WIFI_STA_AUTHMODE_CHANGE,
    ARDUINO_EVENT_WIFI_STA_GOT_IP,
    ARDUINO_EVENT_WIFI_STA_GOT_IP6,
    ARDUINO_EVENT_WIFI_STA_LOST_IP,
    ARDUINO_EVENT_WIFI_AP_START,
    ARDUINO_EVENT_WIFI_AP_STOP,
    ARDUINO_EVENT_WIFI_AP_STACONNECTED,
    ARDUINO_EVENT_WIFI_AP_STADISCONNECTED,
    ARDUINO_EVENT_WIFI_AP_STAIPASSIGNED,
    ARDUINO_EVENT_WIFI_AP_PROBEREQRECVED,
    ARDUINO_EVENT_WIFI_AP_GOT_IP6,
    ARDUINO_EVENT_WIFI_FTM_REPORT,
    ARDUINO_EVENT_ETH_START,
    ARDUINO_EVENT_ETH_STOP,
    ARDUINO_EVENT_ETH_CONNECTED,
    ARDUINO_EVENT_ETH_DISCONNECTED,
    ARDUINO_EVENT_ETH_GOT_IP,
    ARDUINO_EVENT_ETH_GOT_IP6,
    ARDUINO_EVENT_WPS_ER_SUCCESS,
    ARDUINO_EVENT_WPS_ER_FAILED,
    ARDUINO_EVENT_WPS_ER_TIMEOUT,
    ARDUINO_EVENT_WPS_ER_PIN,
    ARDUINO_EVENT_WPS_ER_PBC_OVERLAP,
    ARDUINO_EVENT_SC_SCAN_DONE,
    ARDUINO_EVENT_SC_FOUND_CHANNEL,
    ARDUINO_EVENT_SC_GOT_SSID_PSWD,
    ARDUINO_EVENT_SC_SEND_ACK_DONE,
    ARDUINO_EVENT_PROV_INIT,
    ARDUINO_EVENT_PROV_DEINIT,
    ARDUINO_EVENT_PROV_START,
    ARDUINO_EVENT_PROV_END,
    ARDUINO_EVENT_PROV_CRED_RECV,
    ARDUINO_EVENT_PROV_CRED_FAIL,
    ARDUINO_EVENT_PROV_CRED_SUCCESS,
    ARDUINO_EVENT_MAX
} arduino_event_id_t;

typedef union {
    wifi_event_sta_scan_done_t wifi_scan_done;
    wifi_event_sta_authmode_change_t wifi_sta_authmode_change;
    wifi_event_sta_connected_t wifi_sta_connected;
    wifi_event_sta_disconnected_t wifi_sta_disconnected;
    wifi_event_sta_wps_er_pin_t wps_er_pin;
    wifi_event_sta_wps_fail_reason_t wps_fail_reason;
    wifi_event_ap_probe_req_rx_t wifi_ap_probereqrecved;
    wifi_event_ap_staconnected_t wifi_ap_staconnected;
    wifi_event_ap_stadisconnected_t wifi_ap_stadisconnected;
    wifi_event_ftm_report_t wifi_ftm_report;
    ip_event_ap_staipassigned_t wifi_ap_staipassigned;
    ip_event_got_ip_t got_ip;
    ip_event_got_ip6_t got_ip6;
    smartconfig_event_got_ssid_pswd_t sc_got_ssid_pswd;
    esp_eth_handle_t eth_connected;
    wifi_sta_config_t prov_cred_recv;
    wifi_prov_sta_fail_reason_t prov_fail_reason;
} arduino_event_info_t;

*/
#endif
