gpc123456/SmartClock/src/BatteryIcon.h

#ifndef BATTERYICON_H
#define BATTERYICON_H

#include <Arduino.h>

const PROGMEM uint8_t BatteryIcon_0[] = { /* 0X81,0X01,0X10,0X00,0X08,0X00, */
0XE7,0XE7,0X81,0XBD,0XBD,0XBD,0XBD,0XBD,0XBD,0XBD,0XBD,0XBD,0XBD,0XBD,0XBD,0X81,
};

const PROGMEM uint8_t BatteryIcon_1[]= { /* 0X81,0X01,0X10,0X00,0X08,0X00, */
0XE7,0XE7,0X81,0XBD,0XBD,0XBD,0XBD,0XBD,0XBD,0XBD,0XBD,0XBD,0X81,0X81,0X81,0X81,
};

const PROGMEM uint8_t BatteryIcon_2[]= {/* 0X81,0X01,0X10,0X00,0X08,0X00, */
0XE7,0XE7,0X81,0XBD,0XBD,0XBD,0XBD,0XBD,0XBD,0X81,0X81,0X81,0X81,0X81,0X81,0X81,
};

const PROGMEM uint8_t BatteryIcon_3[]= { /* 0X81,0X01,0X10,0X00,0X08,0X00, */
0XE7,0XE7,0X81,0XBD,0XBD,0XBD,0X81,0X81,0X81,0X81,0X81,0X81,0X81,0X81,0X81,0X81,
};

const PROGMEM uint8_t BatteryIcon_4[]= { /* 0X81,0X01,0X10,0X00,0X08,0X00, */
0XE7,0XE7,0X81,0X81,0X81,0X81,0X81,0X81,0X81,0X81,0X81,0X81,0X81,0X81,0X81,0X81,
};

//REVERSE
const PROGMEM uint8_t REVERSE_BatteryIcon_0[]= {  /* 0X81,0X01,0X10,0X00,0X10,0X00, */
0XF8,0X1F,0XFB,0XDF,0XFB,0XDF,0XFB,0XDF,0XFB,0XDF,0XFB,0XDF,0XFB,0XDF,0XFB,0XDF,
0XFB,0XDF,0XFB,0XDF,0XFB,0XDF,0XFB,0XDF,0XFB,0XDF,0XF8,0X1F,0XFE,0X7F,0XFE,0X7F,
};

const PROGMEM uint8_t REVERSE_BatteryIcon_1[]={/* 0X81,0X01,0X10,0X00,0X10,0X00, */
0XF8,0X1F,0XF8,0X1F,0XF8,0X1F,0XF8,0X1F,0XFB,0XDF,0XFB,0XDF,0XFB,0XDF,0XFB,0XDF,
0XFB,0XDF,0XFB,0XDF,0XFB,0XDF,0XFB,0XDF,0XFB,0XDF,0XF8,0X1F,0XFE,0X7F,0XFE,0X7F,
};

const PROGMEM uint8_t REVERSE_BatteryIcon_2[]= { /* 0X81,0X01,0X10,0X00,0X10,0X00, */
0XF8,0X1F,0XF8,0X1F,0XF8,0X1F,0XF8,0X1F,0XF8,0X1F,0XF8,0X1F,0XF8,0X1F,0XFB,0XDF,
0XFB,0XDF,0XFB,0XDF,0XFB,0XDF,0XFB,0XDF,0XFB,0XDF,0XF8,0X1F,0XFE,0X7F,0XFE,0X7F,
};

const PROGMEM uint8_t REVERSE_BatteryIcon_3[]={  /* 0X81,0X01,0X10,0X00,0X10,0X00, */
0XF8,0X1F,0XF8,0X1F,0XF8,0X1F,0XF8,0X1F,0XF8,0X1F,0XF8,0X1F,0XF8,0X1F,0XF8,0X1F,
0XF8,0X1F,0XF8,0X1F,0XFB,0XDF,0XFB,0XDF,0XFB,0XDF,0XF8,0X1F,0XFE,0X7F,0XFE,0X7F,
};

const PROGMEM uint8_t REVERSE_BatteryIcon_4[]= {/* 0X81,0X01,0X10,0X00,0X10,0X00, */
0XF8,0X1F,0XF8,0X1F,0XF8,0X1F,0XF8,0X1F,0XF8,0X1F,0XF8,0X1F,0XF8,0X1F,0XF8,0X1F,
0XF8,0X1F,0XF8,0X1F,0XF8,0X1F,0XF8,0X1F,0XF8,0X1F,0XF8,0X1F,0XFE,0X7F,0XFE,0X7F,
};

#endif
